Kolya080808/predprof_25-26/3D-модели/сборка скрин.jpg

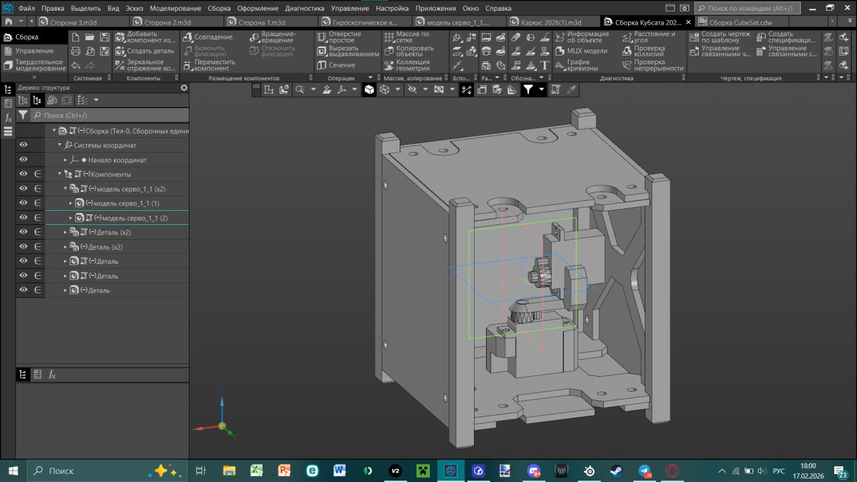
3D-модели/сборка скрин.jpg
