Kolya080808/predprof_25-26/3D-модели/сторона 2 скрин.jpg

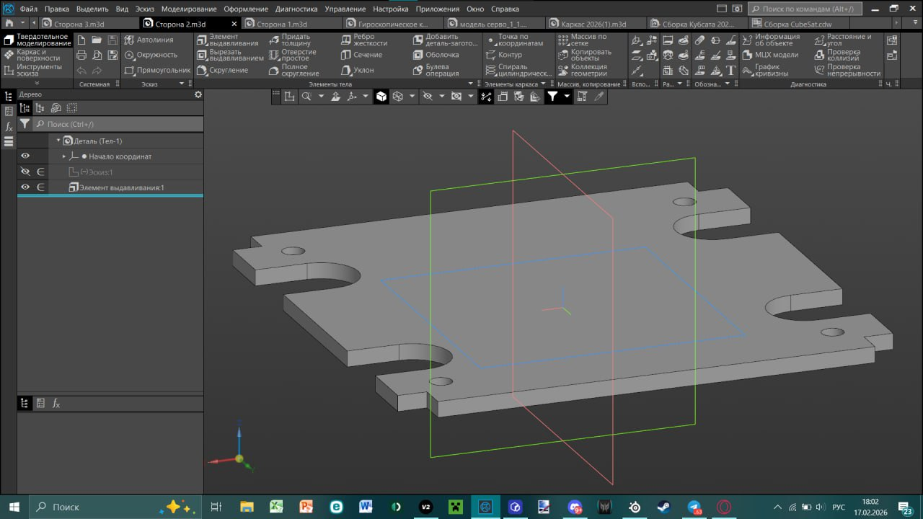
3D-модели/сторона 2 скрин.jpg
