Kolya080808/predprof_25-26/3D-модели/чертеж каркас.jpg

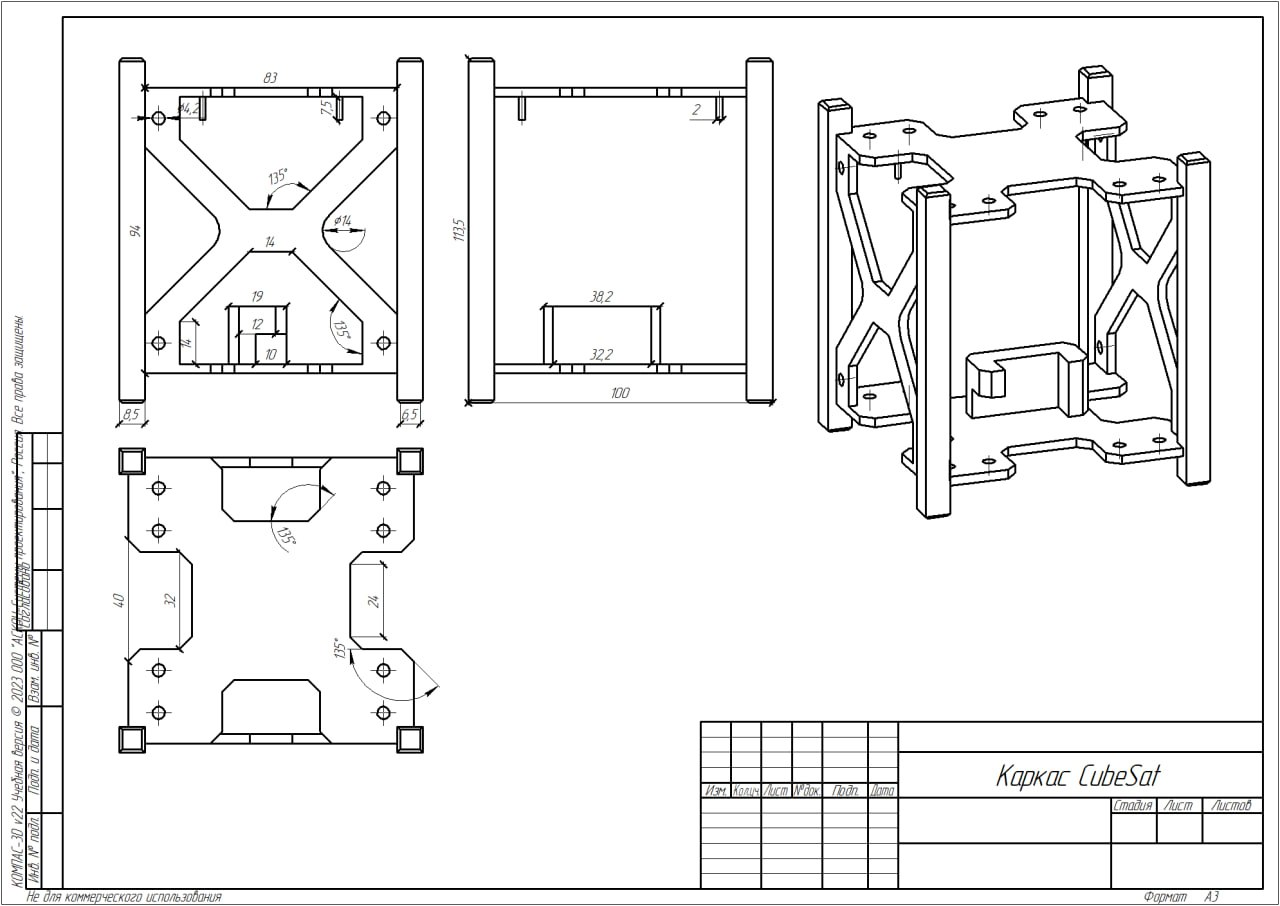
3D-модели/чертеж каркас.jpg
