Kolya080808/predprof_25-26/3D-модели/Чертеж крепление.jpg

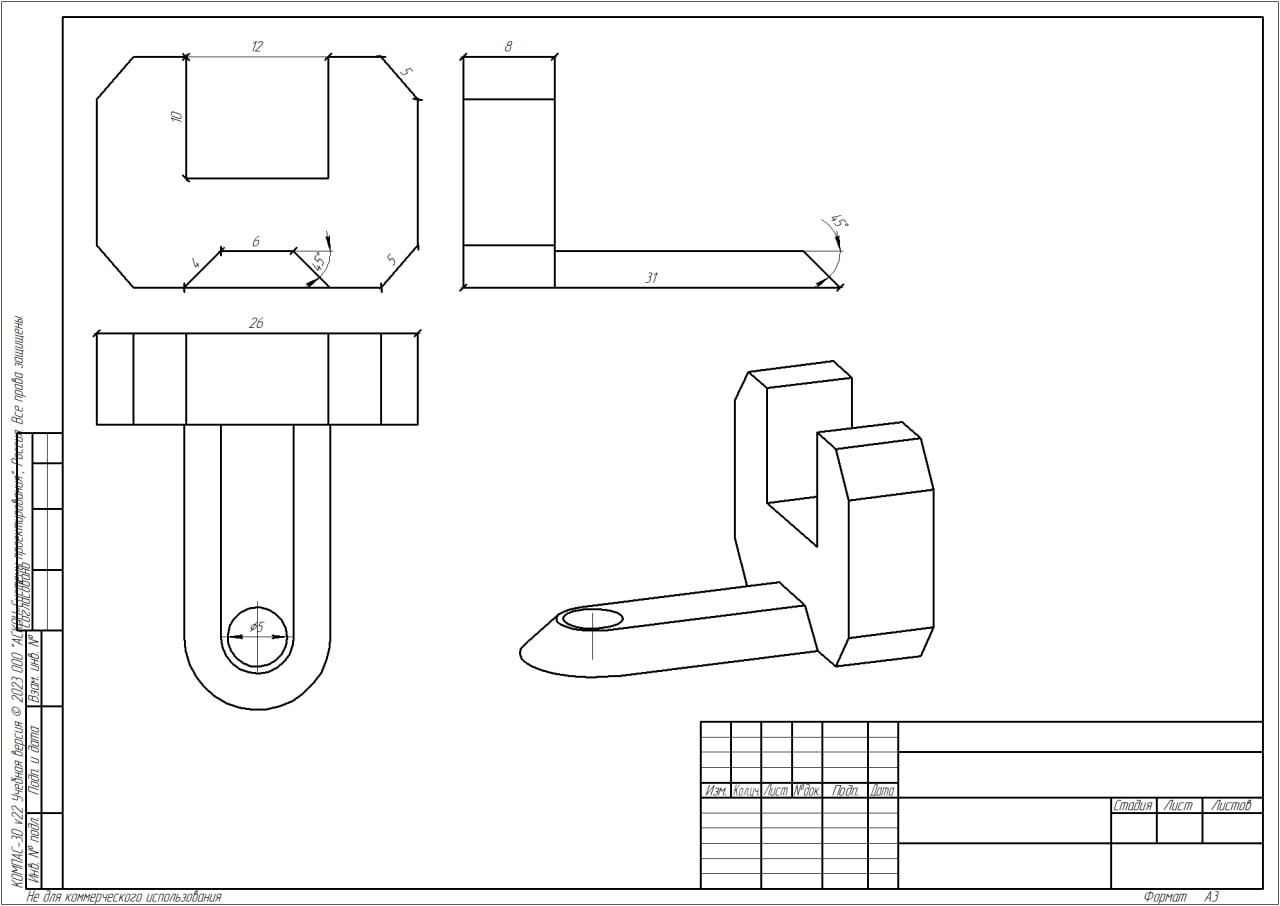
3D-модели/Чертеж крепление.jpg
