Kolya080808/predprof_25-26/3D-модели/чертеж сторона 1.jpg

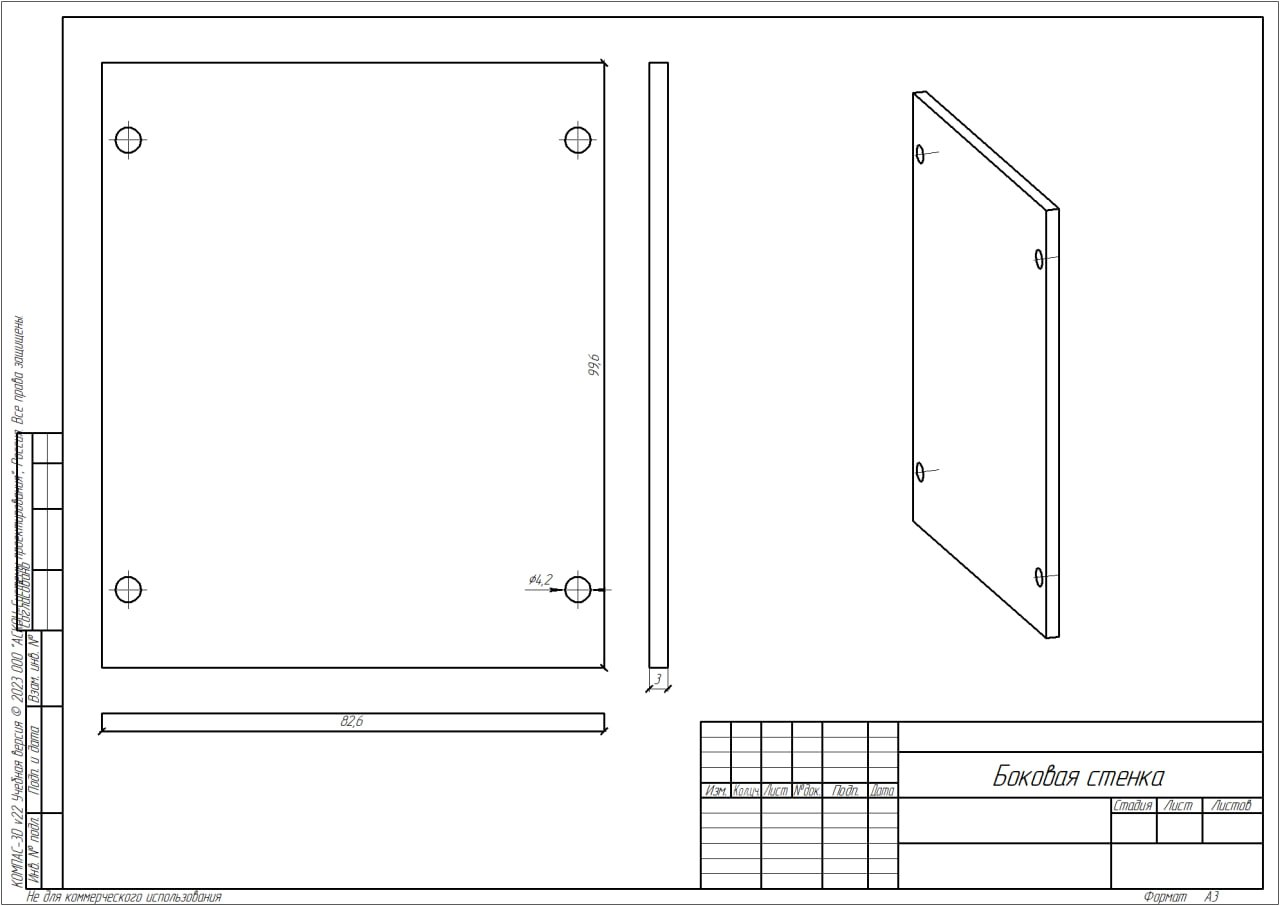
3D-модели/чертеж сторона 1.jpg
