Kolya080808/predprof_25-26/3D-модели/чертеж сторона 2.jpg

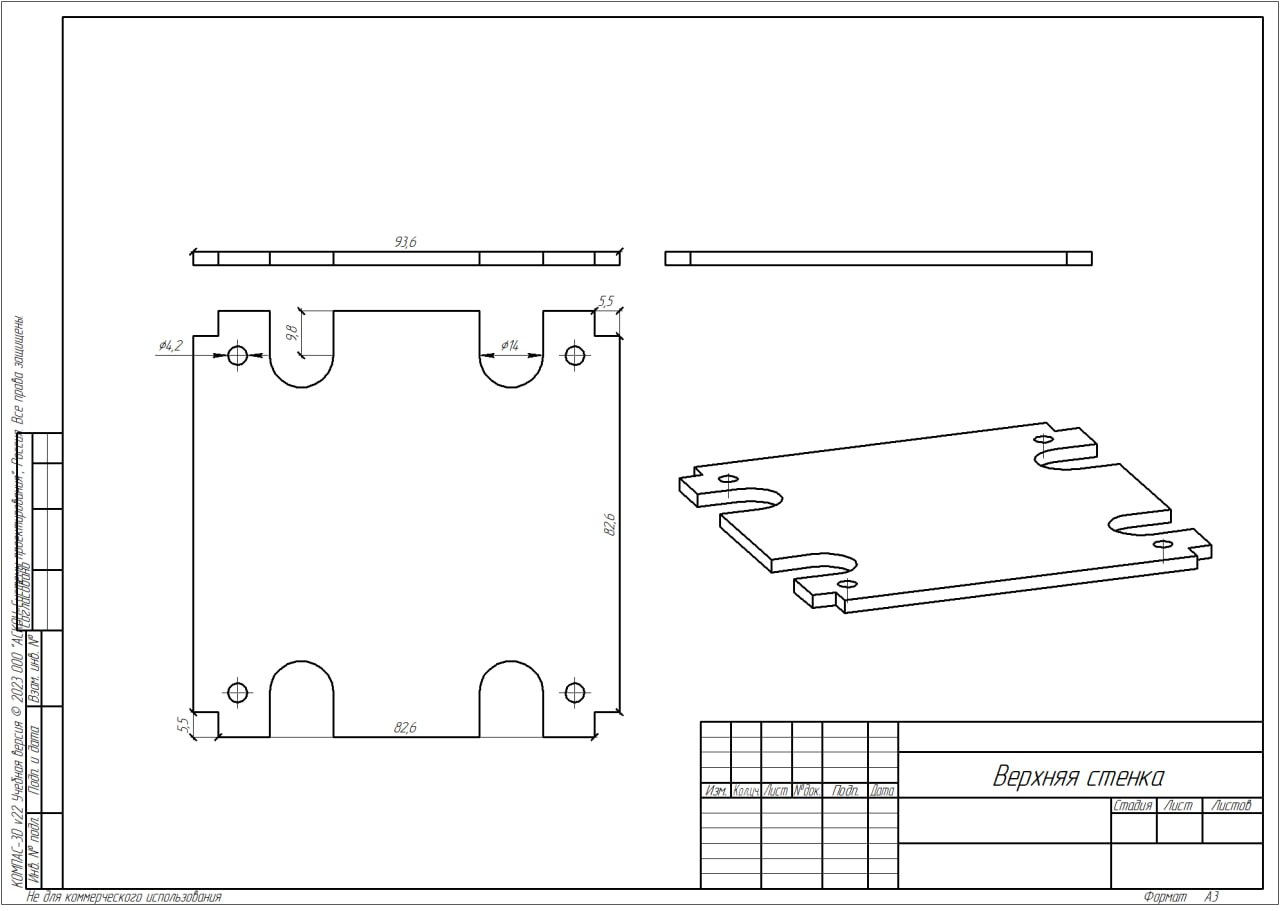
3D-модели/чертеж сторона 2.jpg
