Kolya080808/predprof_25-26/ФотографииСкриншоты/Arduino Nano (CubeSat 1U).jpg

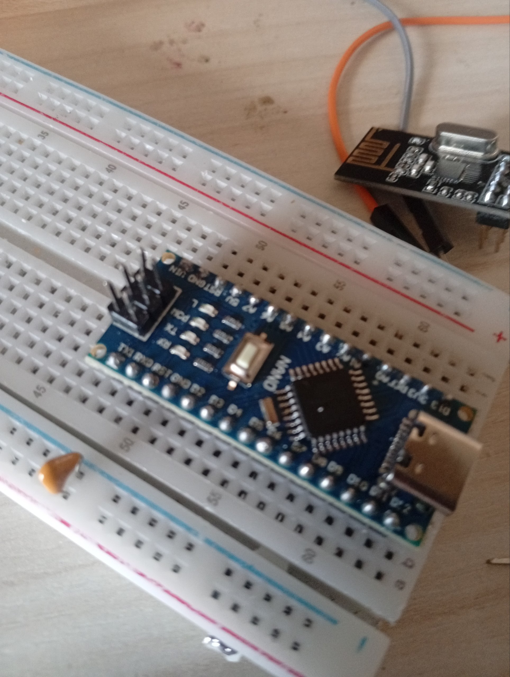
ФотографииСкриншоты/Arduino Nano (CubeSat 1U).jpg
