Kolya080808/predprof_25-26/ФотографииСкриншоты/KY-008 Laser.jpg

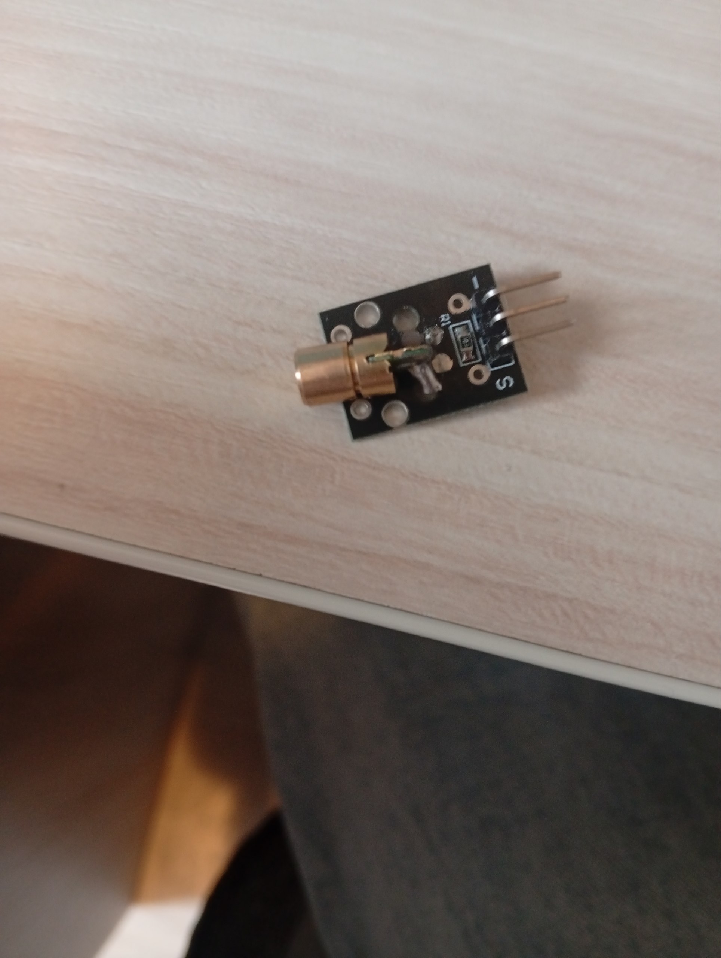
ФотографииСкриншоты/KY-008 Laser.jpg
