Kolya080808/predprof_25-26/ФотографииСкриншоты/nRF24l01.jpg

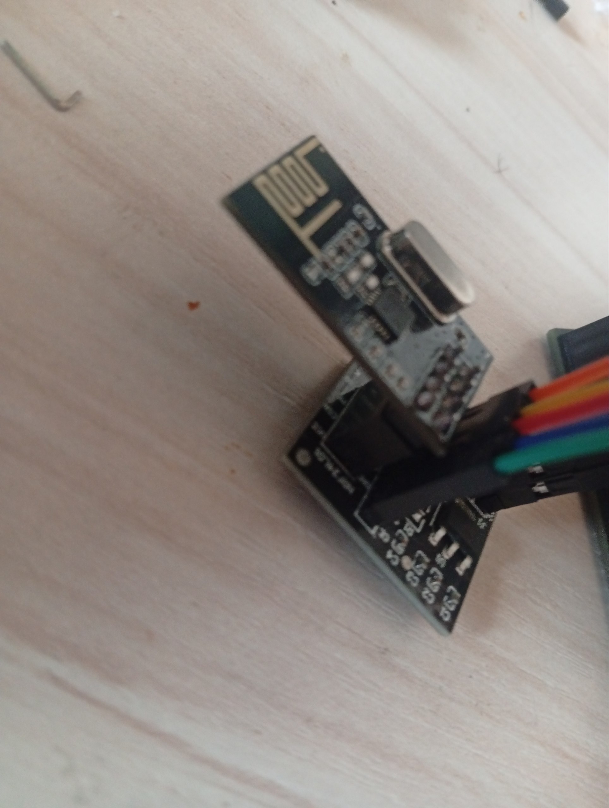
ФотографииСкриншоты/nRF24l01.jpg
