Kolya080808/predprof_25-26/ФотографииСкриншоты/servo 1.jpg

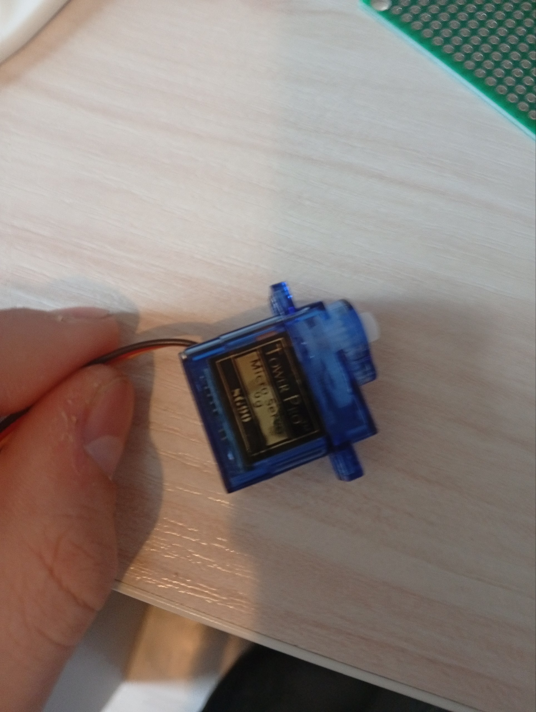
ФотографииСкриншоты/servo 1.jpg
