Kolya080808/predprof_25-26/ФотографииСкриншоты/servo 2.jpg

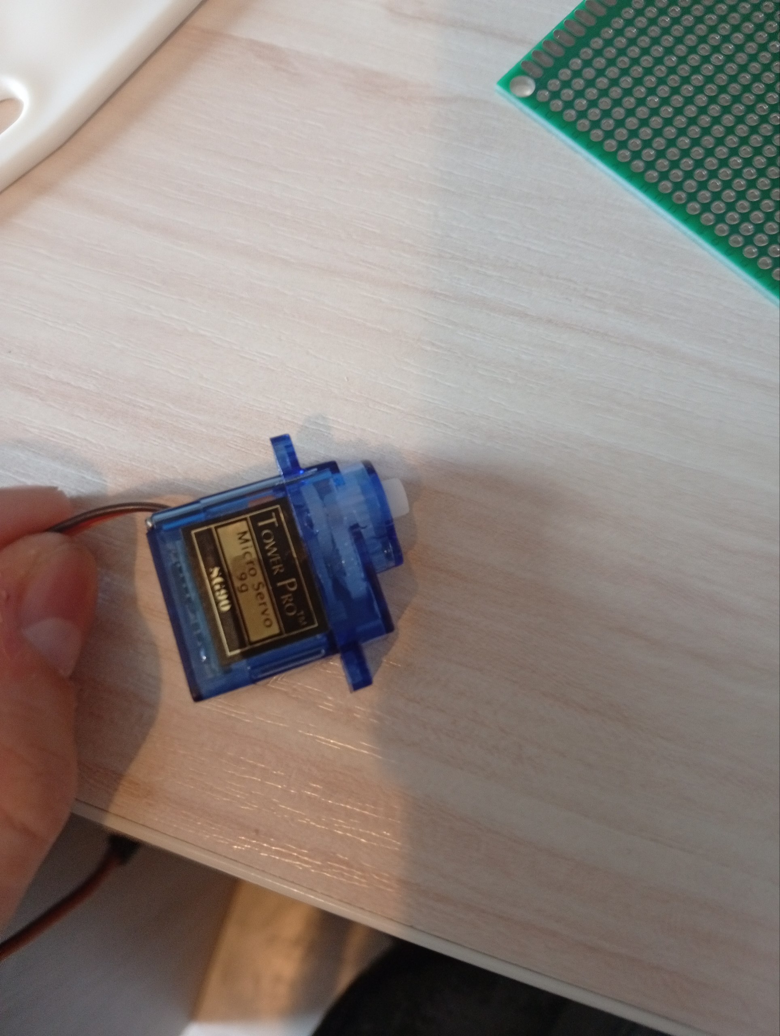
ФотографииСкриншоты/servo 2.jpg
