Kolya080808/predprof_25-26/ФотографииСкриншоты/Кнопка.jpg

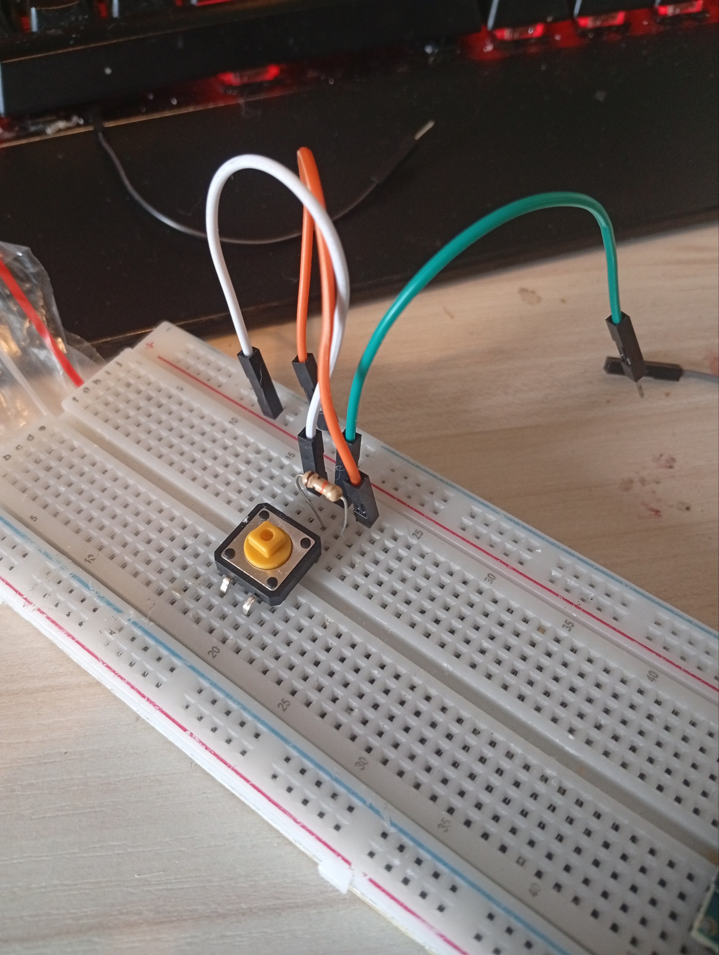
ФотографииСкриншоты/Кнопка.jpg
